pjcau/esp32-emu/model_3d_cover_v1/output/v7/images/assembly_closed_front.png

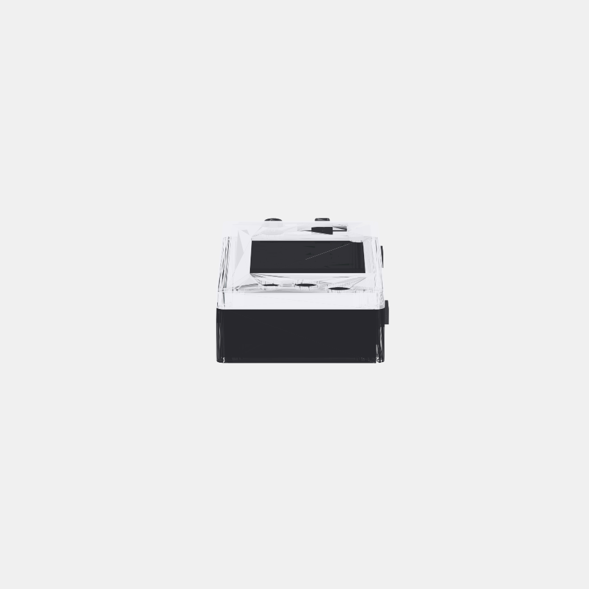
model_3d_cover_v1/output/v7/images/assembly_closed_front.png
