pjcau/esp32-emu/model_3d_cover_v1/output/v7/images/assembly_open_top.png

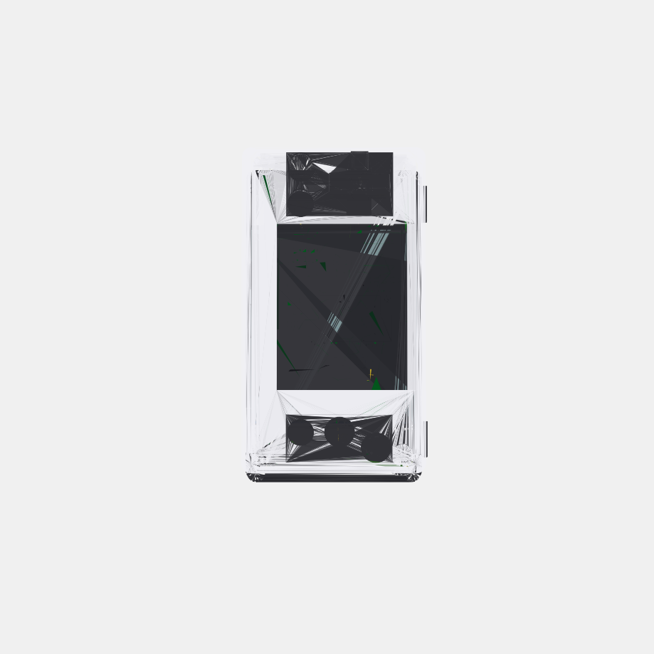
model_3d_cover_v1/output/v7/images/assembly_open_top.png
